YukkuriPannda/roBa/case/v3/tenting/output/tenting_preview.png

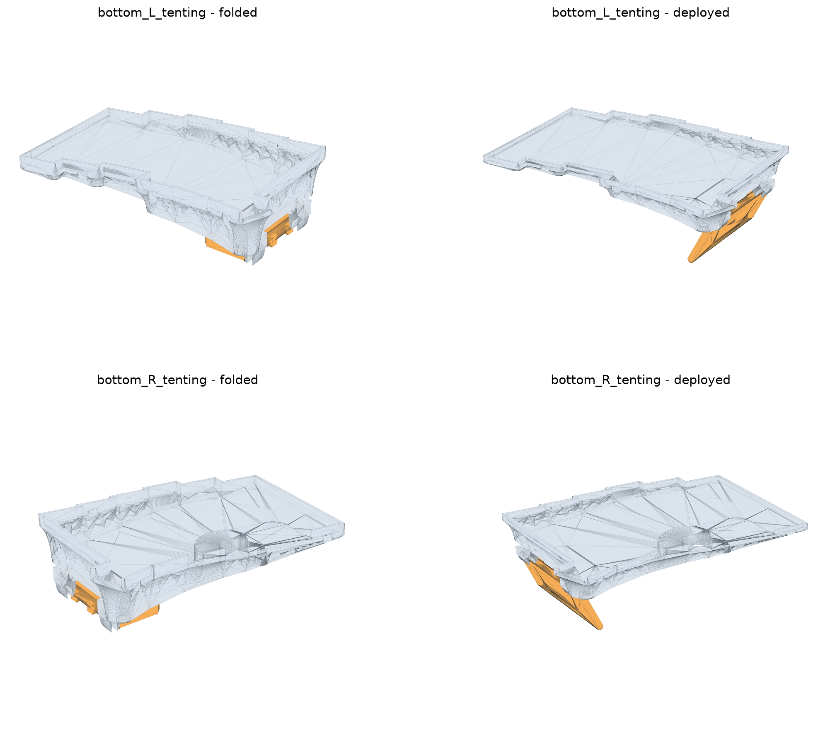
case/v3/tenting/output/tenting_preview.png
